marvertin/voda-septik/firmware/main/voda-septik.cpp

#include "esp_log.h"
#include "freertos/FreeRTOS.h"
#include "freertos/task.h"
#include "esp_timer.h"
#include "nvs_flash.h"
#include "driver/gpio.h"
#include "driver/i2c.h"
#include "esp_rom_sys.h"
#include <stdio.h>
#include "i2cdev.h"
#include "pcf8574.h"

#include "pins.h"
#include "adc_shared.h"
#include "prutokomer.h"
#include "teplota.h"
#include "zasoba.h"
#include "tlak.h"
#include "network_config.h"
#include "system_config.h"
#include "config_store.h"
#include "config_webapp.h"
#include "boot_button.h"
#include "sensor_events.h"
#include "state_manager.h"
#include "network_event_bridge.h"
#include "mqtt_publisher_task.h"
#include "mqtt_commands.h"
#include "mqtt_topics.h"

#include "lcd.h"
#include "network_init.h"
#include "app_error_check.h"
#include "status_display.h"
#include "webapp_startup.h"

#include "esp_partition.h"
#include "esp_ota_ops.h"
#include "esp_netif.h"
#include "esp_task_wdt.h"

extern "C" {
    void cpp_app_main(void);
}

static const char *TAG = "voda_septik";
static constexpr uint32_t TASK_WDT_TIMEOUT_MS = 5000;
static constexpr bool MQTT_BENCH_MODE = false;
static constexpr const char *MQTT_BENCH_URI = "mqtt://amur.veve:1884";
static constexpr const char *MQTT_BENCH_USERNAME = "";
static constexpr const char *MQTT_BENCH_PASSWORD = "";

static esp_err_t task_wdt_init_or_reconfigure(const esp_task_wdt_config_t *cfg)
{
    if (cfg == nullptr) {
        return ESP_ERR_INVALID_ARG;
    }

    const esp_err_t init_result = esp_task_wdt_init(cfg);
    if (init_result == ESP_ERR_INVALID_STATE) {
        return esp_task_wdt_reconfigure(cfg);
    }

    return init_result;
}

static bool is_error_reset_reason(esp_reset_reason_t reason)
{
    switch (reason) {
        case ESP_RST_PANIC:
        case ESP_RST_INT_WDT:
        case ESP_RST_TASK_WDT:
        case ESP_RST_WDT:
        case ESP_RST_BROWNOUT:
        case ESP_RST_PWR_GLITCH:
        case ESP_RST_CPU_LOCKUP:
            return true;
        default:
            return false;
    }
}

static void indicate_error_reset_if_needed(void)
{
    esp_reset_reason_t reason = esp_reset_reason();
    if (!is_error_reset_reason(reason)) {
        return;
    }

    ESP_LOGW(TAG, "Detekovan chybovy reset (reason=%d), spoustim chybovou LED sekvenci", static_cast<int>(reason));

    gpio_reset_pin(STATUS_LED_GPIO);
    gpio_set_direction(STATUS_LED_GPIO, GPIO_MODE_OUTPUT);

    const TickType_t fast_delay = pdMS_TO_TICKS(50);
    const TickType_t fast_total = pdMS_TO_TICKS(10000);
    TickType_t start = xTaskGetTickCount();

    while ((xTaskGetTickCount() - start) < fast_total) {
        gpio_set_level(STATUS_LED_GPIO, 1);
        vTaskDelay(fast_delay);
        gpio_set_level(STATUS_LED_GPIO, 0);
        vTaskDelay(fast_delay);
    }

    gpio_set_level(STATUS_LED_GPIO, 1);
    vTaskDelay(pdMS_TO_TICKS(500));
    gpio_set_level(STATUS_LED_GPIO, 0);
    vTaskDelay(pdMS_TO_TICKS(500));
}

static void log_config_webapp_url(void)
{
    esp_netif_t *ap_netif = esp_netif_get_handle_from_ifkey("WIFI_AP_DEF");
    if (ap_netif != NULL) {
        esp_netif_ip_info_t ip_info = {};
        if (esp_netif_get_ip_info(ap_netif, &ip_info) == ESP_OK && ip_info.ip.addr != 0) {
            ESP_LOGI(TAG, "Konfiguracni aplikace bezi na: http://" IPSTR "/", IP2STR(&ip_info.ip));
            return;
        }
    }

    ESP_LOGI(TAG, "Konfiguracni aplikace bezi na: http://192.168.4.1/");
}

static bool s_ap_switch_done = false;

static void on_boot_button_pressed(void *ctx)
{
    (void)ctx;

    if (s_ap_switch_done) {
        return;
    }

    ESP_LOGW(TAG, "BOOT tlacitko stisknuto, prepinam do konfiguracniho AP rezimu");
    esp_err_t ap_result = network_init_ap("voda-septik-config", "");
    if (ap_result == ESP_OK) {
        s_ap_switch_done = true;
        ESP_LOGI(TAG, "Konfiguracni AP rezim aktivni");
        esp_err_t webapp_result = webapp_startup_start();
        if (webapp_result != ESP_OK) {
            ESP_LOGW(TAG, "Automaticky start konfiguracni webapp po prepnuti do AP selhal: %s", esp_err_to_name(webapp_result));
        }
        vTaskDelay(pdMS_TO_TICKS(300));
        log_config_webapp_url();
    } else {
        ESP_LOGE(TAG, "Prepnuti do AP rezimu selhalo: %s", esp_err_to_name(ap_result));
    }
}

void print_partitions(void)
{
    esp_partition_iterator_t it =
        esp_partition_find(ESP_PARTITION_TYPE_ANY,
                           ESP_PARTITION_SUBTYPE_ANY,
                           NULL);

    while (it != NULL) {
        const esp_partition_t *part =
            esp_partition_get(it);

        printf("Label: %s, Type: %d, Subtype: %d, Addr: 0x%lx, Size: 0x%lx\n",
               part->label,
               part->type,
               part->subtype,
             static_cast<unsigned long>(part->address),
             static_cast<unsigned long>(part->size));

        it = esp_partition_next(it);
    }

    const esp_partition_t *running =  esp_ota_get_running_partition();

    printf("Running from: %s at 0x%lx\n",
       running->label,
         static_cast<unsigned long>(running->address));
}

void cpp_app_main(void)
{
    boot_button_start(BOOT_BUTTON_GPIO, on_boot_button_pressed, nullptr);
    indicate_error_reset_if_needed();
    status_display_init();
    print_partitions();
    esp_err_t nvs_result = nvs_flash_init();
    if (nvs_result == ESP_ERR_NVS_NO_FREE_PAGES || nvs_result == ESP_ERR_NVS_NEW_VERSION_FOUND) {
        APP_ERROR_CHECK("E101", nvs_flash_erase());
        nvs_result = nvs_flash_init();
    }
    APP_ERROR_CHECK("E102", nvs_result);

    ESP_LOGI(TAG, "System bezi v normalnim rezimu");

    const esp_task_wdt_config_t task_wdt_cfg = {
        .timeout_ms = TASK_WDT_TIMEOUT_MS,
        .idle_core_mask = (1U << 0) | (1U << 1),
        .trigger_panic = false,
    };

  APP_ERROR_CHECK("E103", task_wdt_init_or_reconfigure(&task_wdt_cfg));
  ESP_LOGI(TAG,
            "Task watchdog inicializovan: timeout_ms=%lu idle_core_mask=0x%lx panic=1",
             (unsigned long)TASK_WDT_TIMEOUT_MS,
             (unsigned long)task_wdt_cfg.idle_core_mask);

    sensor_events_init(32);
    network_event_bridge_init();

    APP_ERROR_CHECK("E104", config_store_prepare("app_cfg"));

    APP_ERROR_CHECK("E105", config_store_begin_section("Sit"));
    network_config_register_config_items();

    APP_ERROR_CHECK("E106", config_store_begin_section("System"));
    system_config_register_config_items();

    APP_ERROR_CHECK("E107", config_store_begin_section("Teplota"));
    teplota_register_config_items();

    APP_ERROR_CHECK("E108", config_store_begin_section("Zasoba"));
    zasoba_register_config_items();

    APP_ERROR_CHECK("E109", config_store_begin_section("Tlak"));
    tlak_register_config_items(); 

    APP_ERROR_CHECK("E119", config_store_begin_section("Prutokomer"));
    prutokomer_register_config_items();

    APP_ERROR_CHECK("E110", config_webapp_prepare("app_cfg"));

    char wifi_ssid[32] = {0};
    char wifi_password[64] = {0};
    char mqtt_uri[128] = {0};
    char mqtt_username[64] = {0};
    char mqtt_password[128] = {0};
    APP_ERROR_CHECK("E111", network_config_load_wifi_credentials(wifi_ssid, sizeof(wifi_ssid), wifi_password, sizeof(wifi_password)));
    APP_ERROR_CHECK("E112", network_config_load_mqtt_uri(mqtt_uri, sizeof(mqtt_uri)));
    APP_ERROR_CHECK("E113", network_config_load_mqtt_credentials(mqtt_username, sizeof(mqtt_username), mqtt_password, sizeof(mqtt_password)));

    if (MQTT_BENCH_MODE) {
        snprintf(mqtt_uri, sizeof(mqtt_uri), "%s", MQTT_BENCH_URI);
        snprintf(mqtt_username, sizeof(mqtt_username), "%s", MQTT_BENCH_USERNAME);
        snprintf(mqtt_password, sizeof(mqtt_password), "%s", MQTT_BENCH_PASSWORD);
        ESP_LOGW(TAG,
                 "MQTT_BENCH_MODE je aktivni, prepisuji MQTT cfg: uri=%s user=%s password_set=%s",
                 mqtt_uri,
                 (mqtt_username[0] != '\0') ? mqtt_username : "(none)",
                 (mqtt_password[0] != '\0') ? "yes" : "no");
    }
    
    const mqtt_topic_descriptor_t *status_topic_desc = mqtt_topic_descriptor(mqtt_topic_id_t::TOPIC_SYSTEM_STATUS);
    APP_ERROR_CHECK("E114", status_topic_desc != nullptr ? ESP_OK : ESP_ERR_INVALID_STATE);

    network_mqtt_lwt_config_t lwt_cfg = {
        .enabled = true,
        .status_topic = status_topic_desc->full_topic,
        .qos = 1,
        .retain = true,
    };


    ESP_LOGI(TAG,
             "MQTT cfg pred pripojenim: uri=%s, user=%s, password_set=%s, status_topic=%s",
             mqtt_uri,
             (mqtt_username[0] != '\0') ? mqtt_username : "(none)",
             (mqtt_password[0] != '\0') ? "yes" : "no",
             status_topic_desc->full_topic);
    APP_ERROR_CHECK("E116", network_init_with_mqtt_ex(wifi_ssid,
                                                        wifi_password,
                                                        mqtt_uri,
                                                        mqtt_username,
                                                        mqtt_password,
                                                        &lwt_cfg));

    APP_ERROR_CHECK("E117", mqtt_publisher_task_start(32, 4, configMINIMAL_STACK_SIZE * 6));
    APP_ERROR_CHECK("E118", mqtt_commands_start());


    
    lcd_init(); // Inicializace LCD před spuštěním ostatních úloh, aby mohly ihned zobrazovat informace

    state_manager_start();

    adc_shared_init();
    
    // initialize sensor producer tasks
    prutokomer_init();

    // vytvoření paralelních tasků
    teplota_init();
    zasoba_init();
    tlak_init();


}
